Festo-se/raeware/perception-modules/realsense/cam-holder.stl

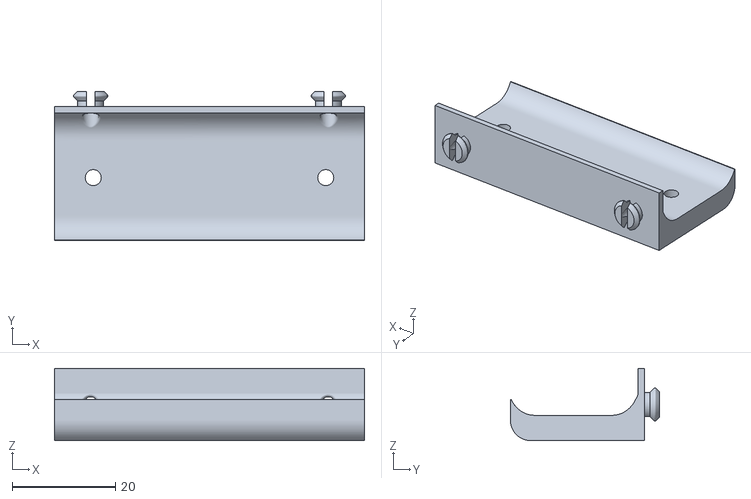
[picture p33: CAD file, 2021-06-02]
perception-modules/realsense/cam-holder.stl
60.0 x 28.9 x 14.0
