Festo-se/raeware/vacuum-modules/double/top.stl

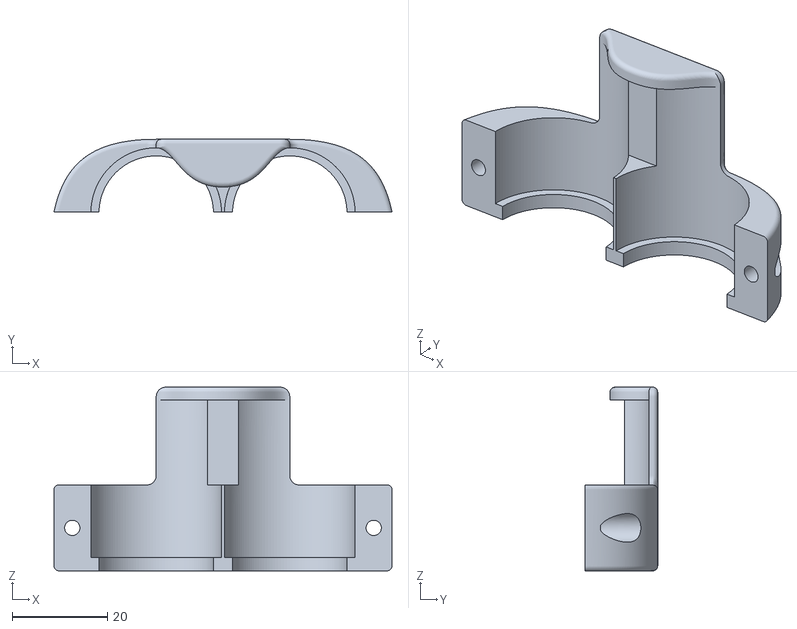
[picture p34: CAD file, 2021-06-02]
vacuum-modules/double/top.stl
70.9 x 15.2 x 38.5
