Festo-se/raeware/base-system/guide-parts-metal/trapezodial-guide.stl

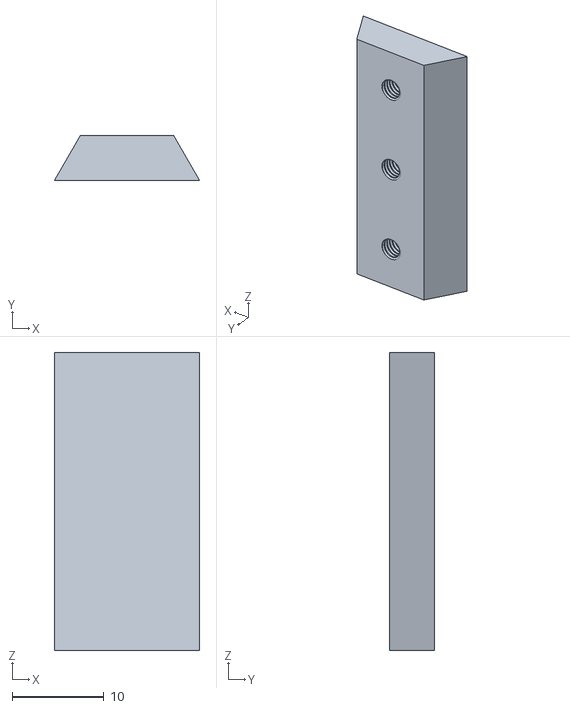
[picture p35: CAD file, 2021-08-18]
base-system/guide-parts-metal/trapezodial-guide.stl
15.8 x 4.85 x 32.4
