Festo-se/raeware/base-system/guide-parts-nylon/trapezodial-guide.stl

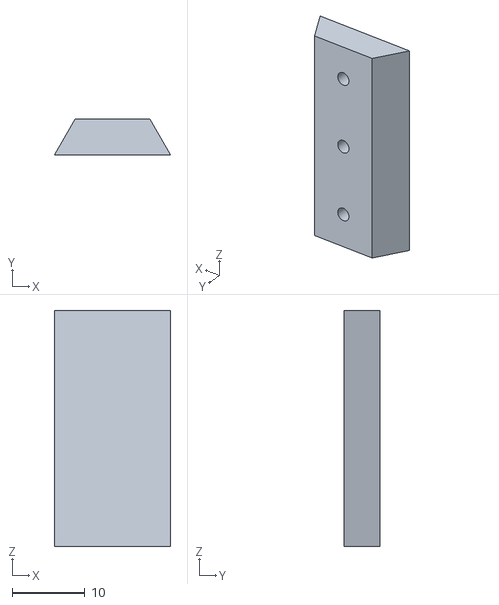
[picture p36: CAD file, 2021-08-27]
base-system/guide-parts-nylon/trapezodial-guide.stl
15.9 x 4.90 x 32.4
