Festo-se/raeware/base-system/lynxmotion-system/clipsed-case-bottom.stl

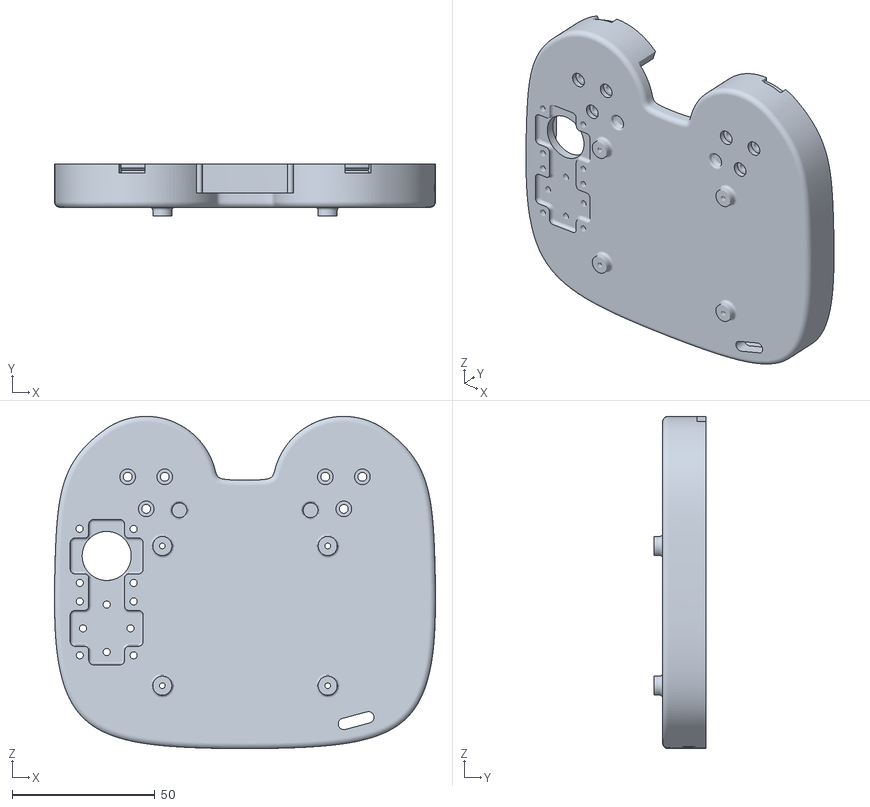
[picture p37: CAD file, 2021-08-18]
base-system/lynxmotion-system/clipsed-case-bottom.stl
133.6 x 18.3 x 116.5
