Festo-se/raeware/gripper-modules/radialgripper80/top_left.stl

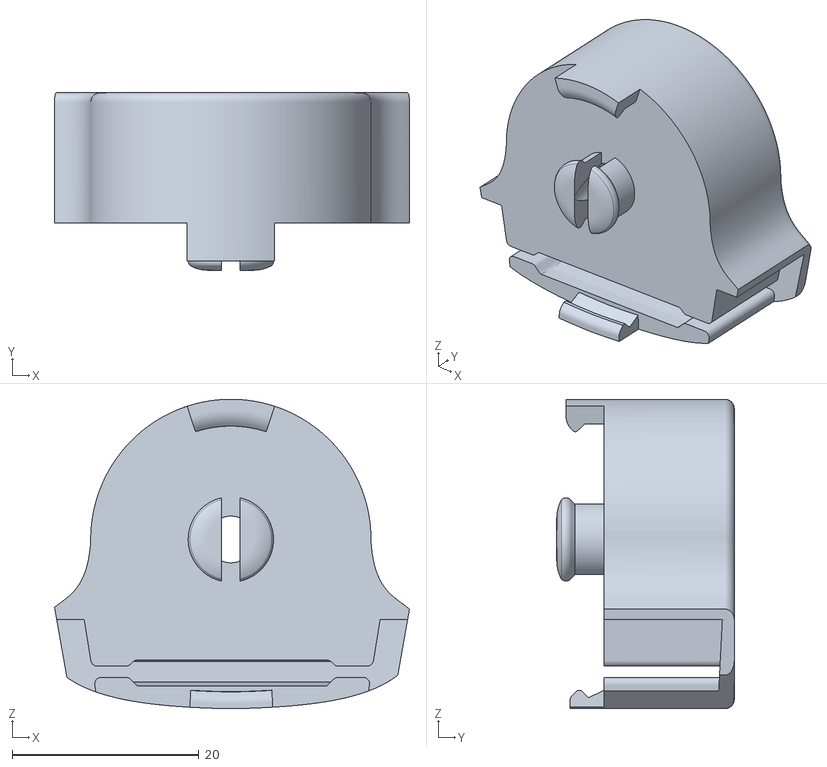
[picture p38: CAD file, 2021-07-19]
gripper-modules/radialgripper80/top_left.stl
38.0 x 19.0 x 33.1
