Festo-se/raeware/base-system/drive-parts/rack.stl

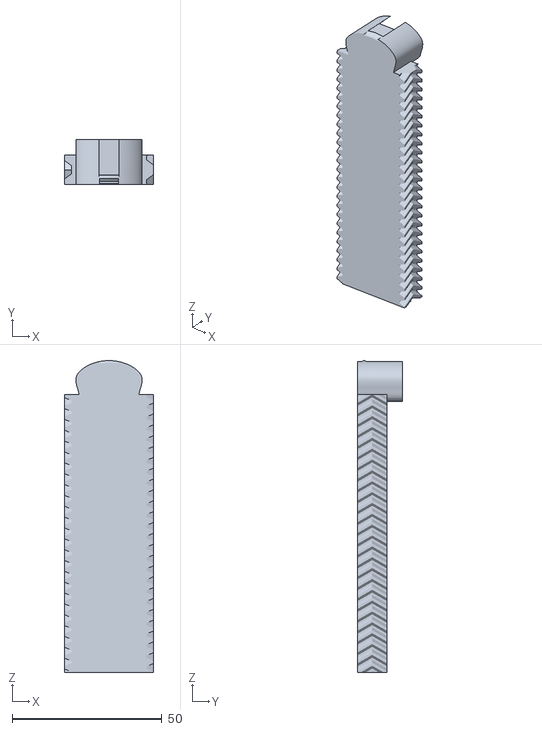
[picture p39: CAD file, 2021-08-18]
base-system/drive-parts/rack.stl
29.7 x 15.2 x 104.3
