Festo-se/raeware/base-system/lynxmotion-system/rpi-case.stl

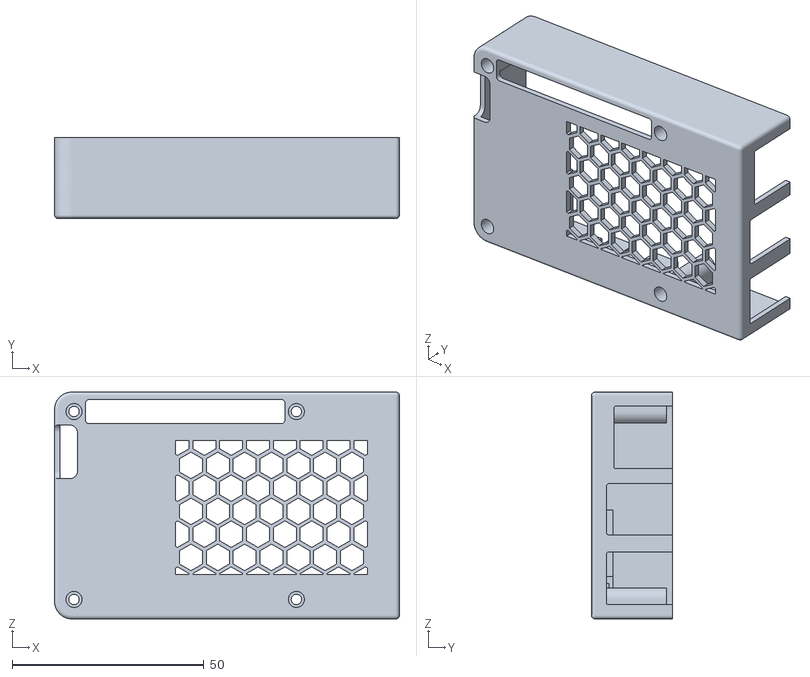
[picture p40: CAD file, 2021-06-02]
base-system/lynxmotion-system/rpi-case.stl
90.0 x 21.2 x 59.2
